Neil-Sawhney/N2-Iambic-Paddle/img/image-2.png

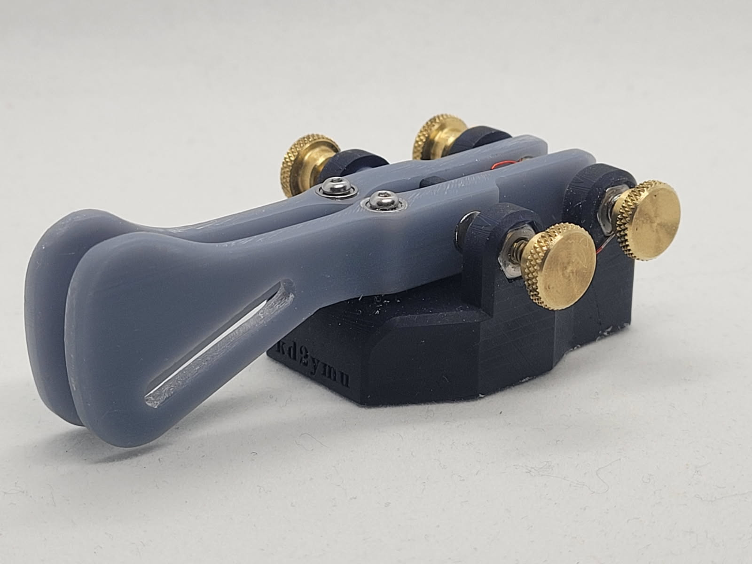
img/image-2.png
